irissonnlima/yggi-keyboard/hardware/stagger-mechanism/renders/100pct_stagger.png

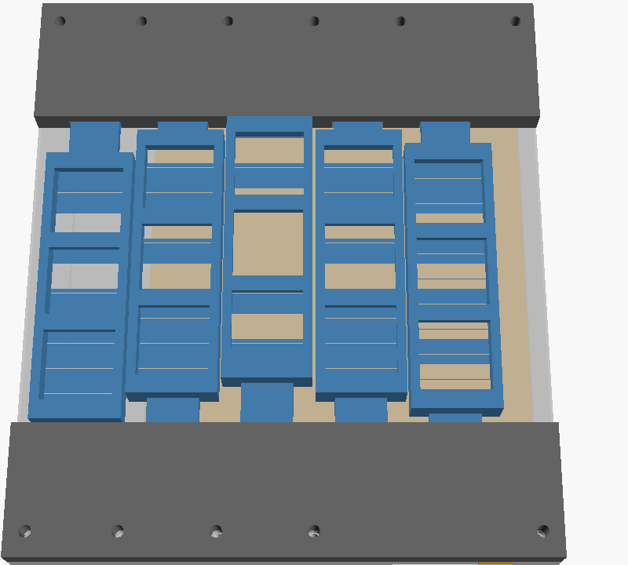
hardware/stagger-mechanism/renders/100pct_stagger.png
