irissonnlima/yggi-keyboard/hardware/stagger-mechanism/renders/v2/v2_0pct.png

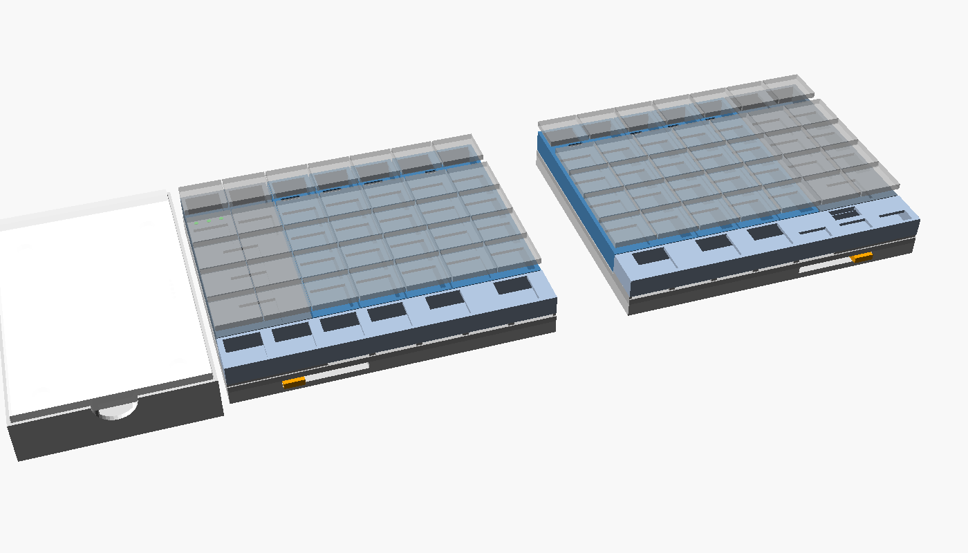
hardware/stagger-mechanism/renders/v2/v2_0pct.png
