irissonnlima/yggi-keyboard/hardware/stagger-mechanism/renders/v2/v2_left_explodida.png

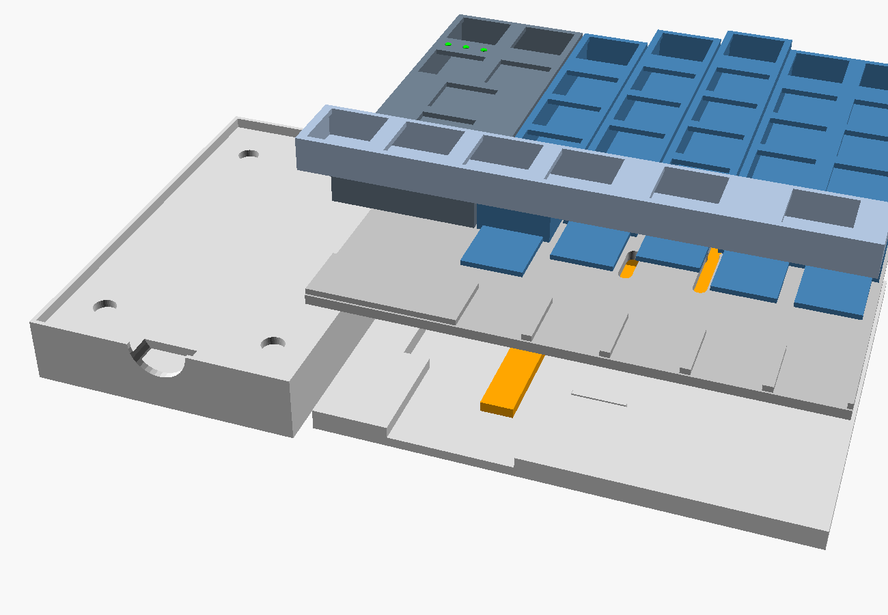
hardware/stagger-mechanism/renders/v2/v2_left_explodida.png
